shrideh/LUNGSTORS/electronics/PROCESS_BOARD_TH/images/PROCESS_BOARD_TH_3.png

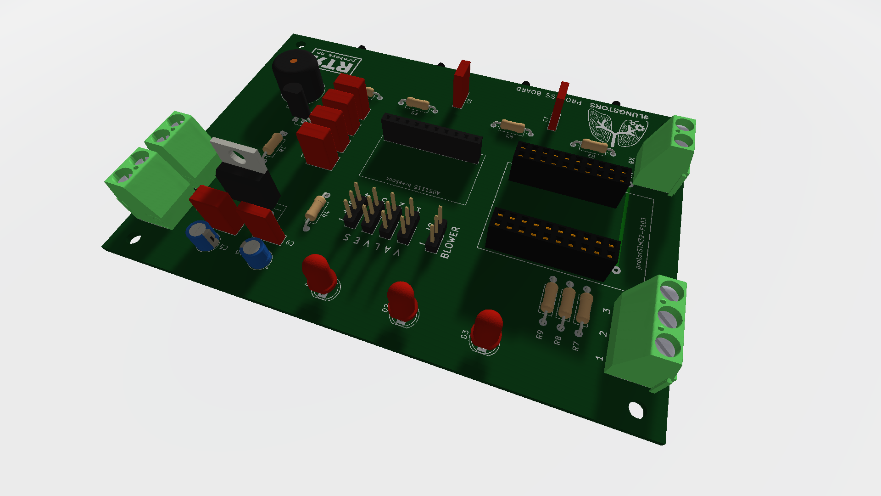
electronics/PROCESS_BOARD_TH/images/PROCESS_BOARD_TH_3.png
