shrideh/LUNGSTORS/models/compressor_assembly/impeler.stl

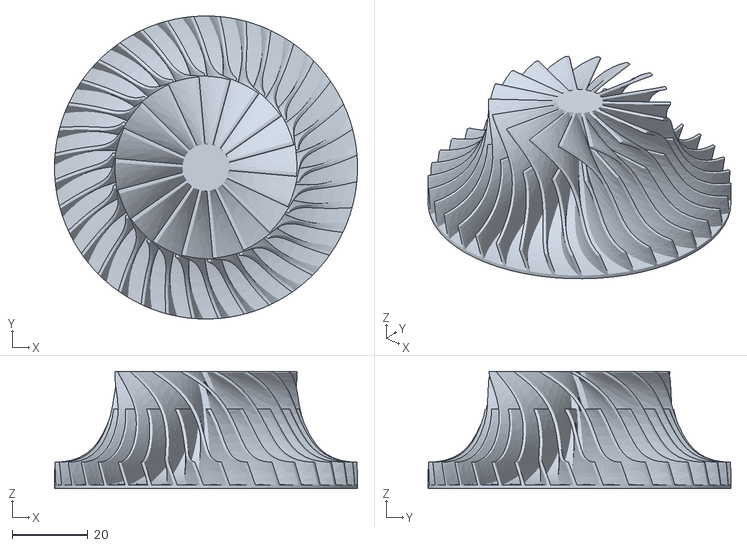
[picture p25: CAD file, 2020-05-02]
models/compressor_assembly/impeler.stl
80.0 x 80.0 x 31.0
