shrideh/LUNGSTORS/models/servo_valve_assembly/hose_connector.step

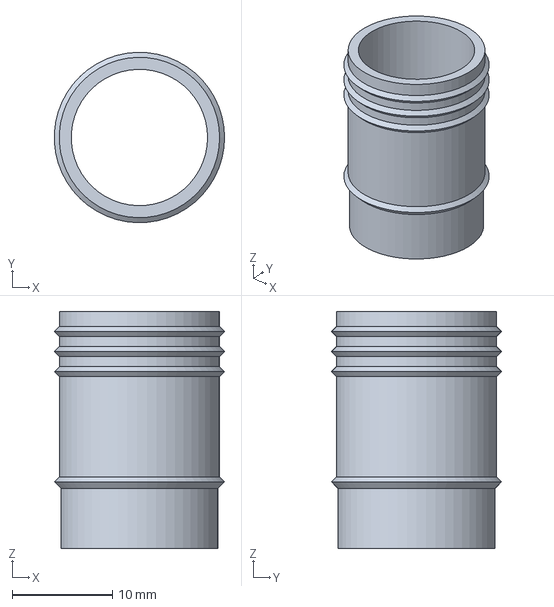
[picture p26: CAD file, 2020-05-02]
models/servo_valve_assembly/hose_connector.step
17.0 x 17.0 x 23.6 mm
