shrideh/LUNGSTORS/models/compressor_assembly/volute_bottom.step

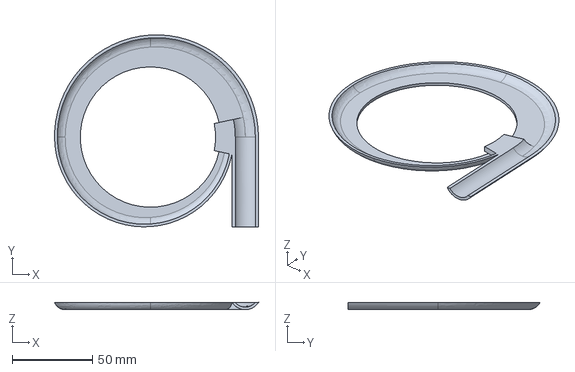
[picture p27: CAD file, 2020-05-02]
models/compressor_assembly/volute_bottom.step
126.8 x 119.5 x 4.60 mm
