shrideh/LUNGSTORS/models/servo_valve_assembly/ball.step

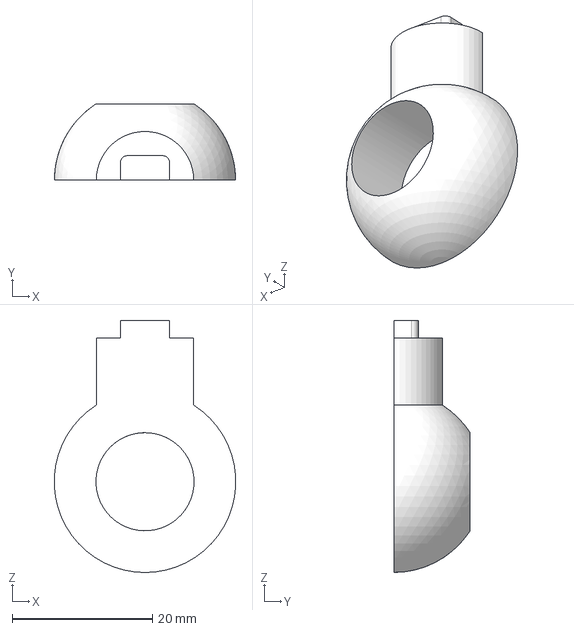
[picture p28: CAD file, 2020-05-02]
models/servo_valve_assembly/ball.step
25.9 x 10.9 x 36.0 mm
