shrideh/LUNGSTORS/models/servo_valve_assembly/servo.step

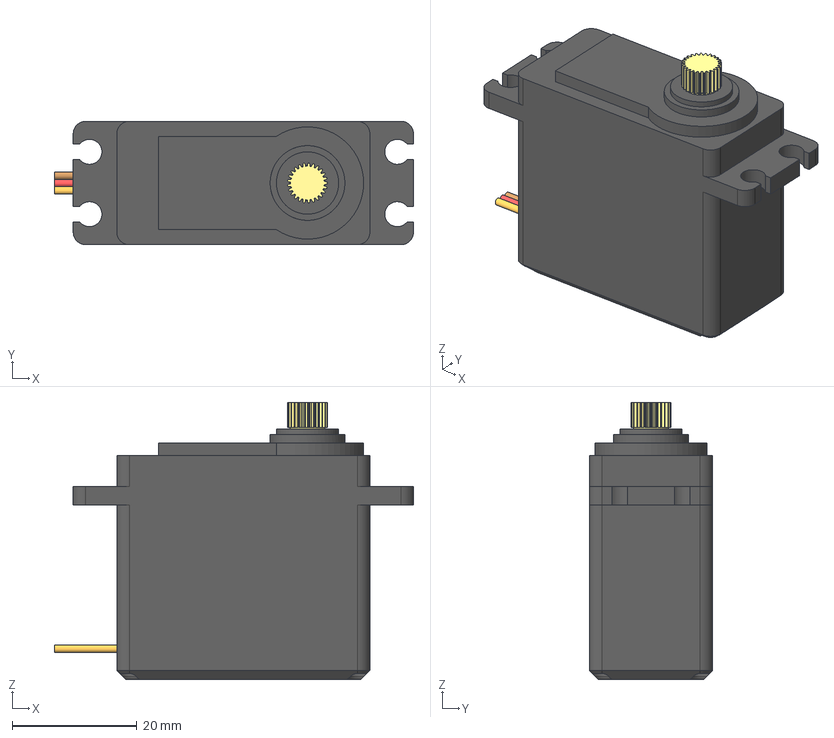
[picture p29: CAD file, 2020-05-02]
models/servo_valve_assembly/servo.step
57.6 x 19.8 x 44.5 mm
