shrideh/LUNGSTORS/models/compressor_assembly/motor_base.step

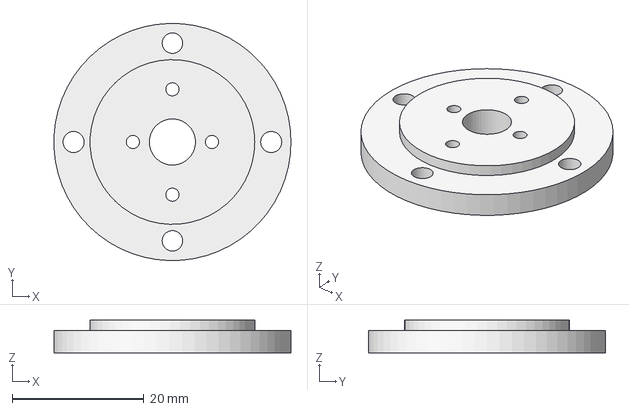
[picture p30: CAD file, 2020-05-02]
models/compressor_assembly/motor_base.step
36.0 x 36.0 x 5.00 mm
