shrideh/LUNGSTORS/models/compressor_assembly/images/blower.gif

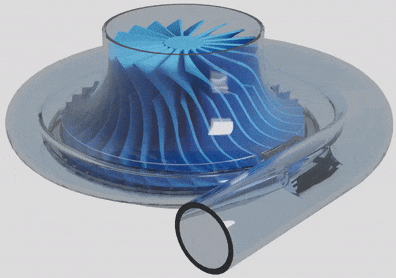
models/compressor_assembly/images/blower.gif
