shrideh/LUNGSTORS/models/compressor_assembly/images/lungstors_blower_1.JPG

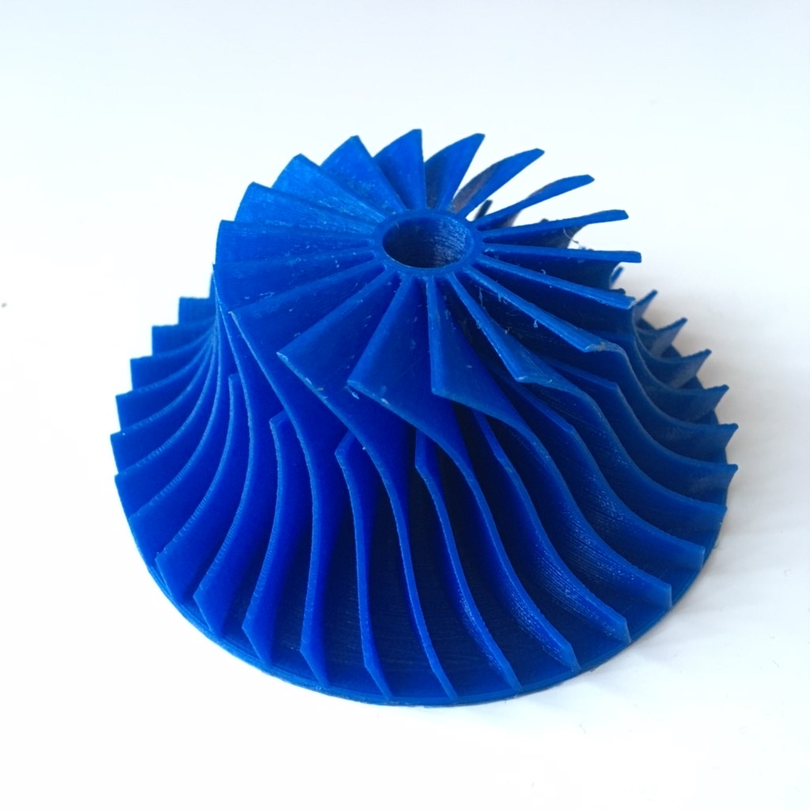
models/compressor_assembly/images/lungstors_blower_1.JPG
