shrideh/LUNGSTORS/models/compressor_assembly/images/lungstors_blower_4.JPG

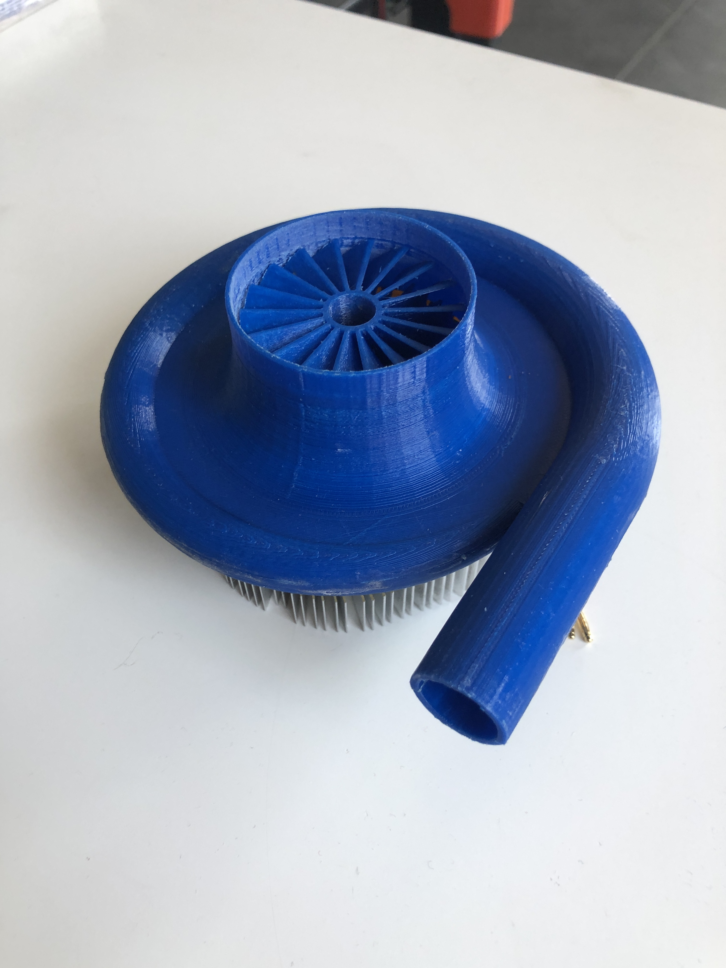
models/compressor_assembly/images/lungstors_blower_4.JPG
