shrideh/LUNGSTORS/models/compressor_assembly/images/lungstors_blower_large.gif

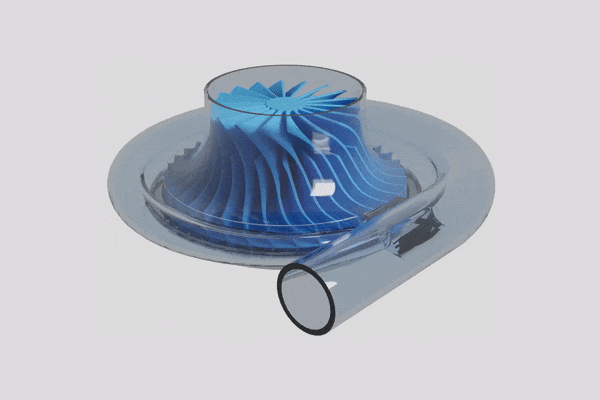
models/compressor_assembly/images/lungstors_blower_large.gif
