shrideh/LUNGSTORS/models/flowmeter_assembly/images/lungstor_flowmeter_1.png

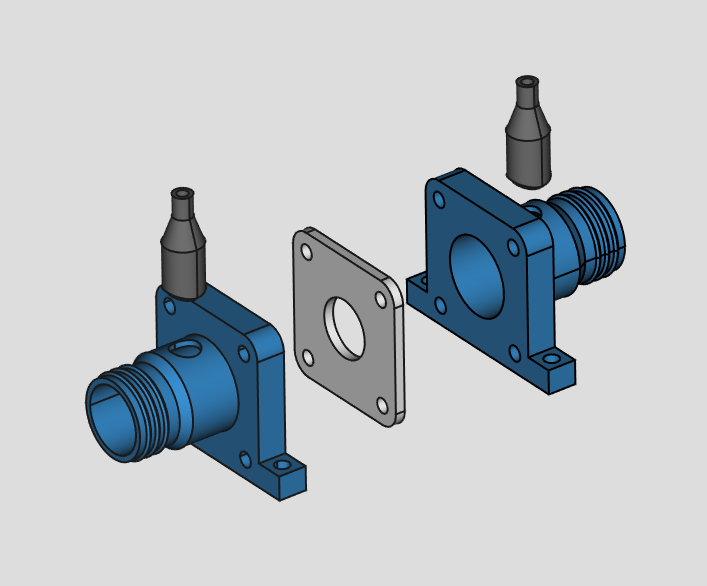
models/flowmeter_assembly/images/lungstor_flowmeter_1.png
