shrideh/LUNGSTORS/models/flowmeter_assembly/images/lungstor_flowmeter_2.JPG

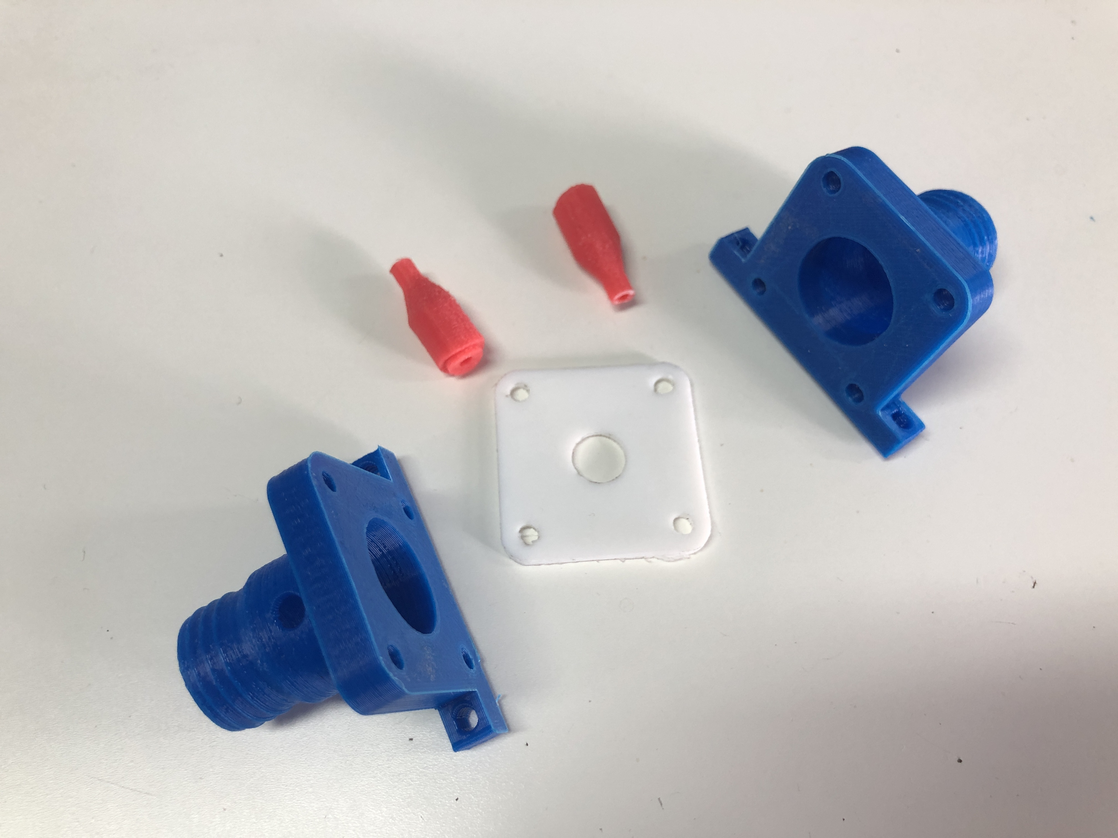
models/flowmeter_assembly/images/lungstor_flowmeter_2.JPG
