shrideh/LUNGSTORS/models/flowmeter_assembly/images/lungstor_flowmeter_3.png

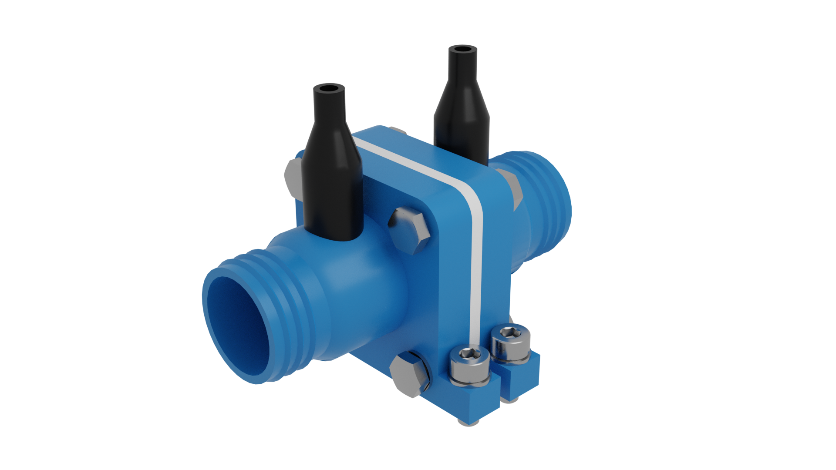
models/flowmeter_assembly/images/lungstor_flowmeter_3.png
