shrideh/LUNGSTORS/models/servo_valve_assembly/images/lungstors_servo_valve_2.JPG

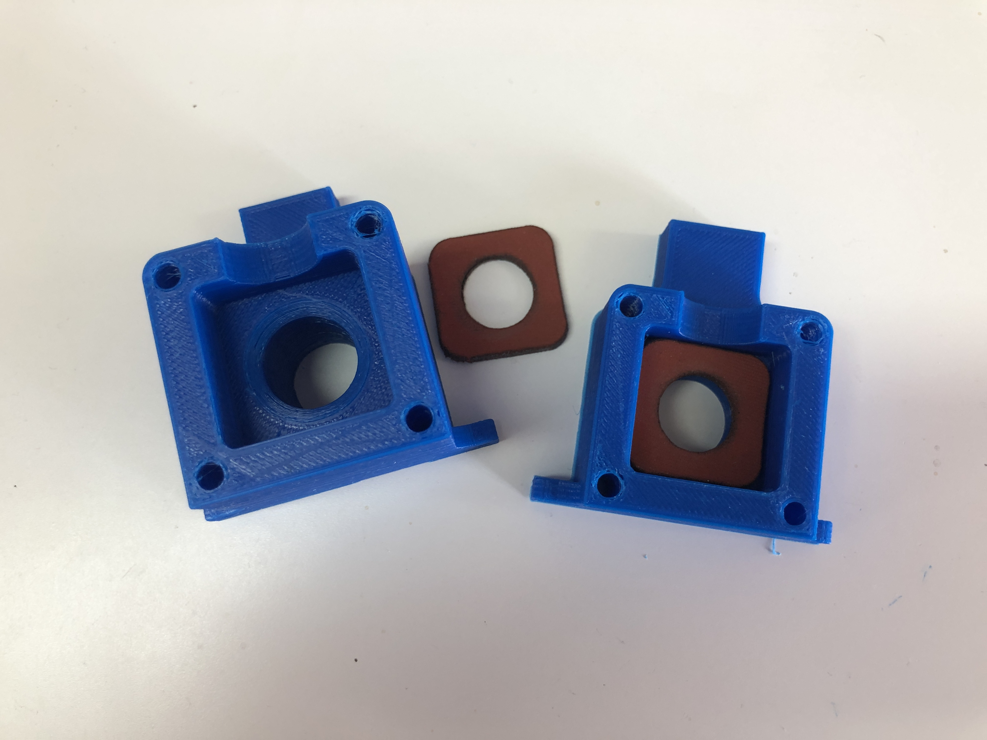
models/servo_valve_assembly/images/lungstors_servo_valve_2.JPG
