shrideh/LUNGSTORS/models/servo_valve_assembly/images/lungstors_servo_valve_3.png

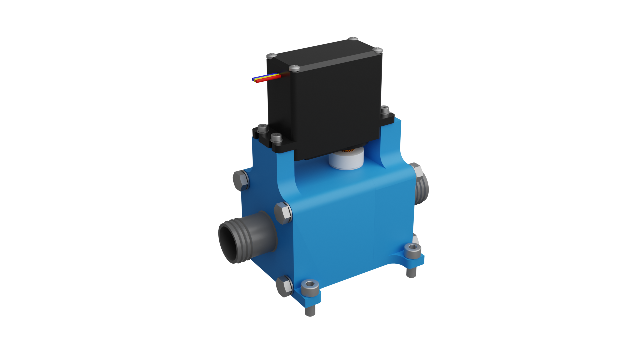
models/servo_valve_assembly/images/lungstors_servo_valve_3.png
