shrideh/LUNGSTORS/models/servo_valve_assembly/images/lungstors_servo_valve_large.gif

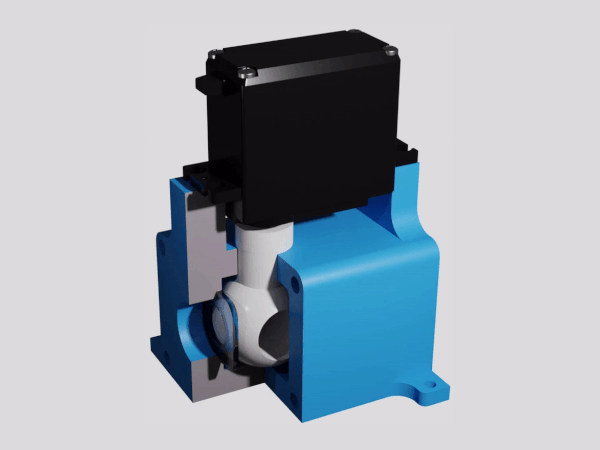
models/servo_valve_assembly/images/lungstors_servo_valve_large.gif
